saidlab-team/RefiBot/hardware/Ball_Holder.png

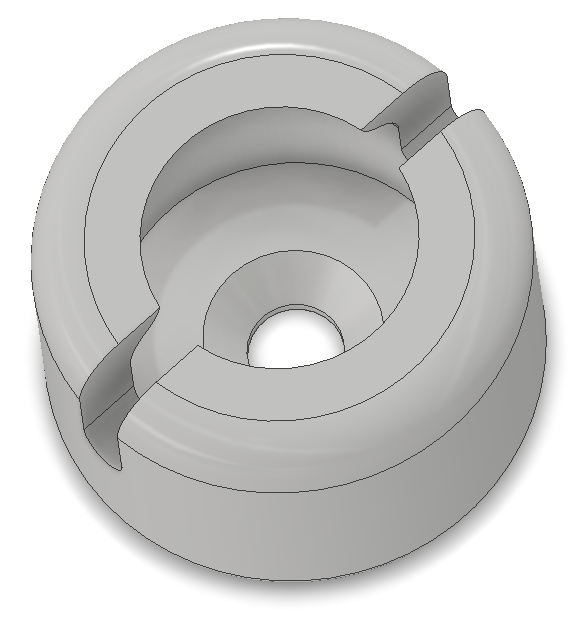
hardware/Ball_Holder.png
