saidlab-team/RefiBot/hardware/Bottom_Plate.png

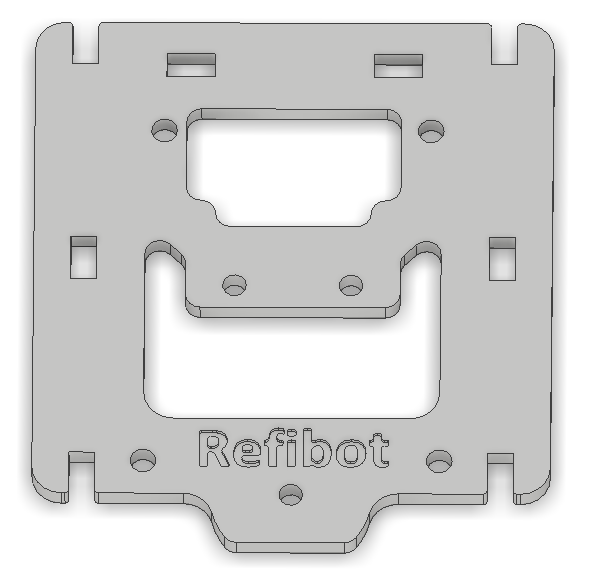
hardware/Bottom_Plate.png
