saidlab-team/RefiBot/hardware/Protective_Plate.png

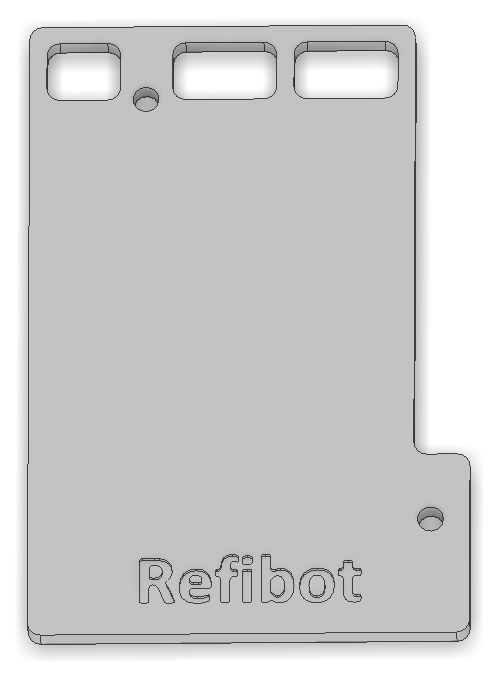
hardware/Protective_Plate.png
