saidlab-team/RefiBot/hardware/Robot_Stand.png

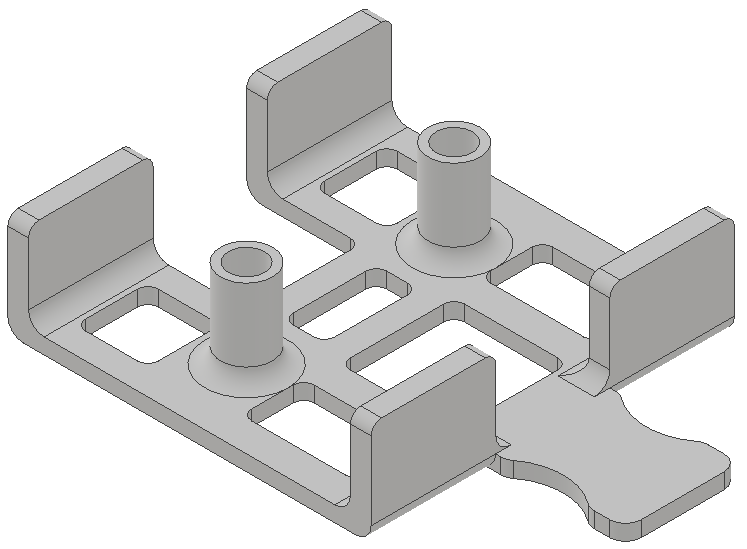
hardware/Robot_Stand.png
