saidlab-team/RefiBot/hardware/Wheel_L_Disk.png

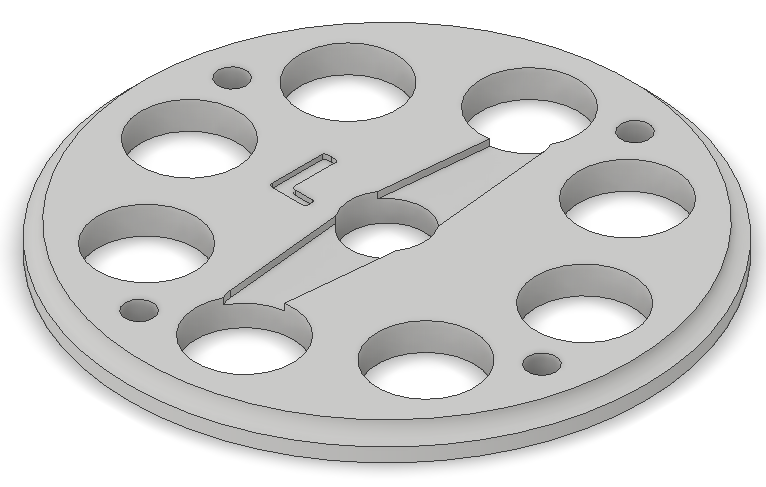
hardware/Wheel_L_Disk.png
