saidlab-team/RefiBot/hardware/Wheel_R_Disk.png

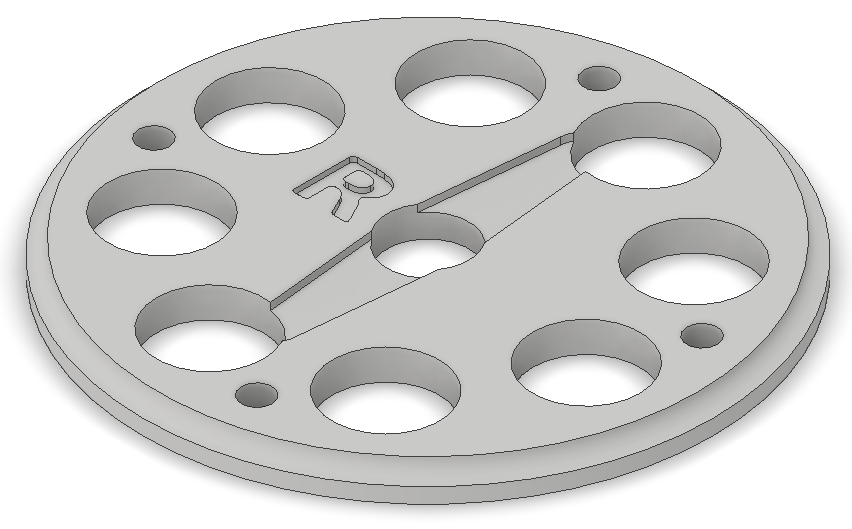
hardware/Wheel_R_Disk.png
